ArduinoNanoProjects/UltraTouch-SX/NextionDisplay/UltraTouchSX-LCARS_2019/Data/Settings/Brightness/UltraTouchSX-LCARS_Brightness_0.png

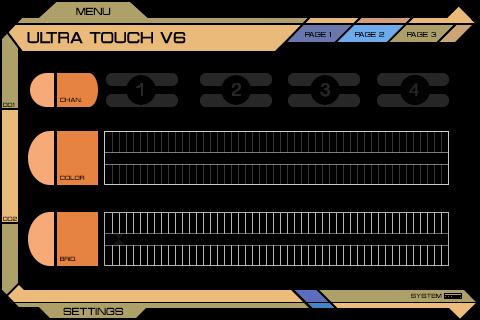
NextionDisplay/UltraTouchSX-LCARS_2019/Data/Settings/Brightness/UltraTouchSX-LCARS_Brightness_0.png
