ArduinoNanoProjects/UltraTouch-SX/NextionDisplay/UltraTouchSX-LCARS_2019/Data/Settings/Brightness/UltraTouchSX-LCARS_Brightness_1.png

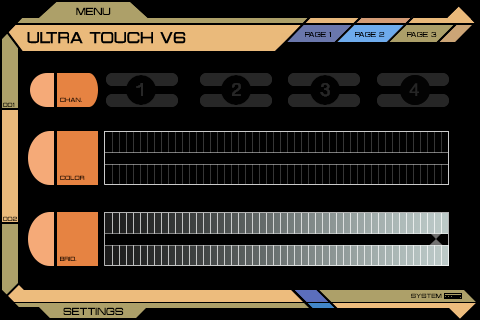
NextionDisplay/UltraTouchSX-LCARS_2019/Data/Settings/Brightness/UltraTouchSX-LCARS_Brightness_1.png
