ArduinoNanoProjects/UltraTouch-SX/NextionDisplay/UltraTouchSX-LCARS_2019/Data/Settings/Channel/UltraTouchSX-Channel1.png

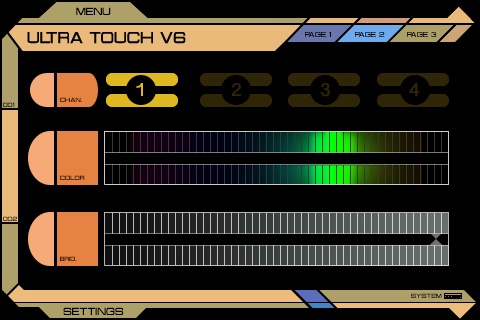
NextionDisplay/UltraTouchSX-LCARS_2019/Data/Settings/Channel/UltraTouchSX-Channel1.png
