ArduinoNanoProjects/UltraTouch-SX/NextionDisplay/UltraTouchSX-LCARS_2019/Data/Settings/Channel/UltraTouchSX-Channel3.png

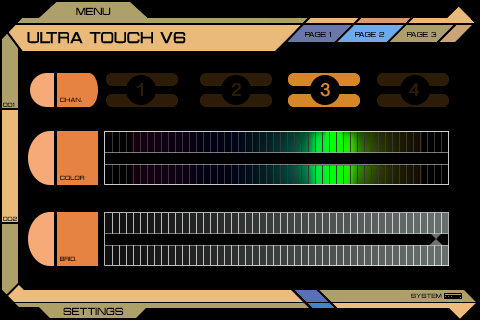
NextionDisplay/UltraTouchSX-LCARS_2019/Data/Settings/Channel/UltraTouchSX-Channel3.png
