ArduinoNanoProjects/UltraTouch-SX/NextionDisplay/UltraTouchSX-LCARS_2019/Data/Settings/Coloring/UltraTouchSX-LCARS_Color-Blau.png

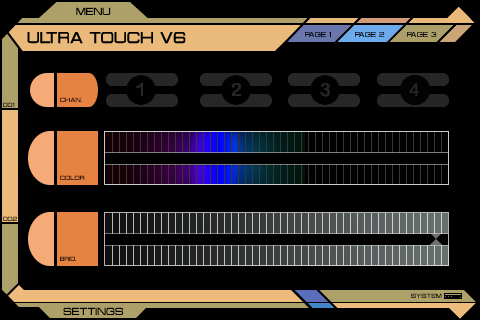
NextionDisplay/UltraTouchSX-LCARS_2019/Data/Settings/Coloring/UltraTouchSX-LCARS_Color-Blau.png
