ArduinoNanoProjects/UltraTouch-SX/NextionDisplay/UltraTouchSX-LCARS_2019/Data/Welcome/UltraTouchSX-LCARS_Welcome.png

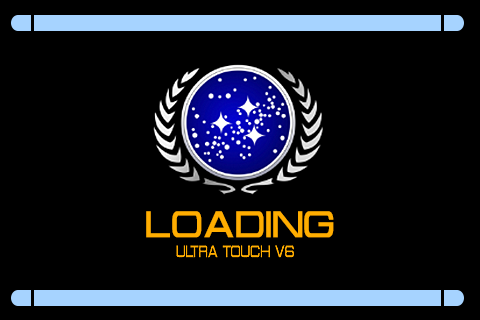
NextionDisplay/UltraTouchSX-LCARS_2019/Data/Welcome/UltraTouchSX-LCARS_Welcome.png
