ArduinoNanoProjects/UltraTouch-SX/NextionDisplay/UltraTouchSX-U4_2020/Design-UltraTouch SX6 US4/Screens/Loading-GIF_Home/UltraTouchSX-US4_LodingHome-007.png

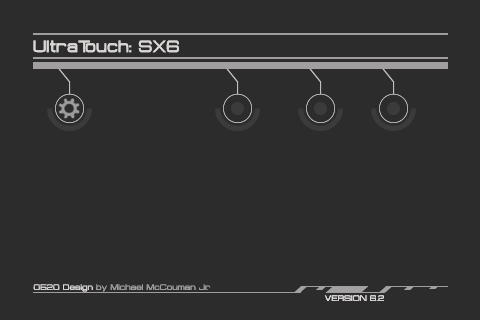
NextionDisplay/UltraTouchSX-U4_2020/Design-UltraTouch SX6 US4/Screens/Loading-GIF_Home/UltraTouchSX-US4_LodingHome-007.png
