ArduinoNanoProjects/UltraTouch-SX/NextionDisplay/UltraTouchSX-U4_2020/Design-UltraTouch SX6 US4/Screens/Page_Radio/UltraTouchSX-US4_Radio-Start_001.png

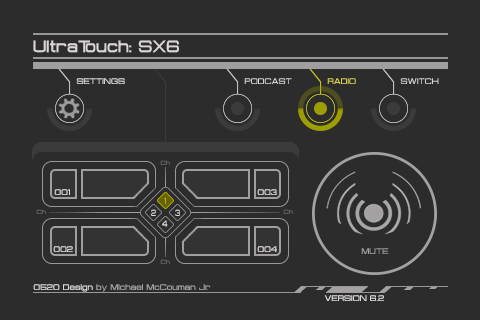
NextionDisplay/UltraTouchSX-U4_2020/Design-UltraTouch SX6 US4/Screens/Page_Radio/UltraTouchSX-US4_Radio-Start_001.png
