ArduinoNanoProjects/UltraTouch-SX/NextionDisplay/UltraTouchSX-U4_2020/Design-UltraTouch SX6 US4/Screens/Page_Settings/Brightness/UltraTouchSX-Brightness_OFF.png

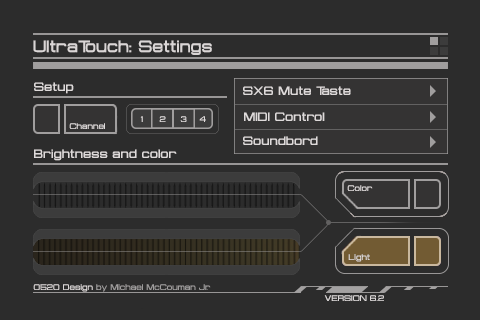
NextionDisplay/UltraTouchSX-U4_2020/Design-UltraTouch SX6 US4/Screens/Page_Settings/Brightness/UltraTouchSX-Brightness_OFF.png
