ArduinoNanoProjects/UltraTouch-SX/NextionDisplay/UltraTouchSX-U4_2020/Design-UltraTouch SX6 US4/Screens/Page_Settings/Coloring/UltraTouchSX-ColorALL.png

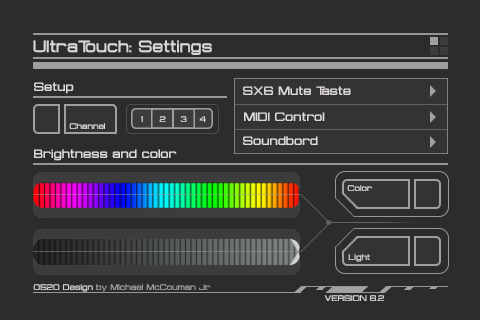
NextionDisplay/UltraTouchSX-U4_2020/Design-UltraTouch SX6 US4/Screens/Page_Settings/Coloring/UltraTouchSX-ColorALL.png
